afiskon/hbr-8b/images/front-panel.jpg

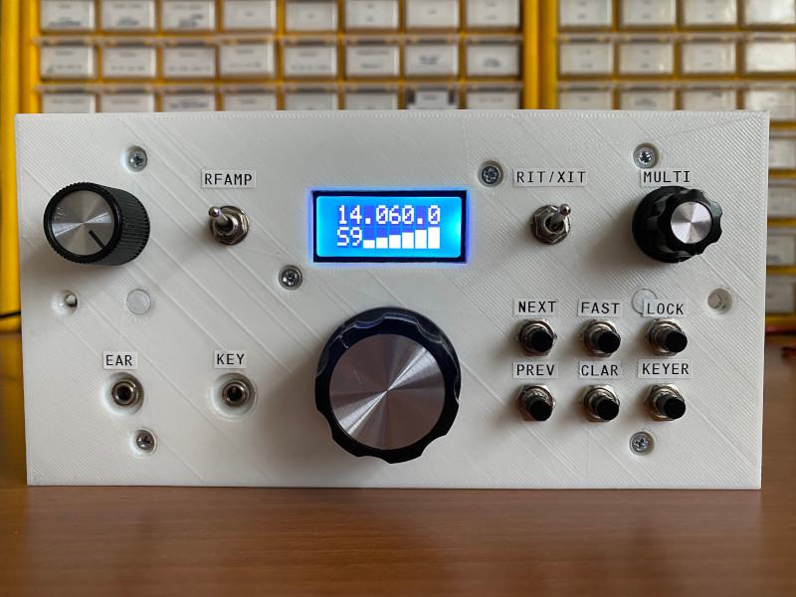
images/front-panel.jpg
