afiskon/hbr-8b/images/bpfs/10.png

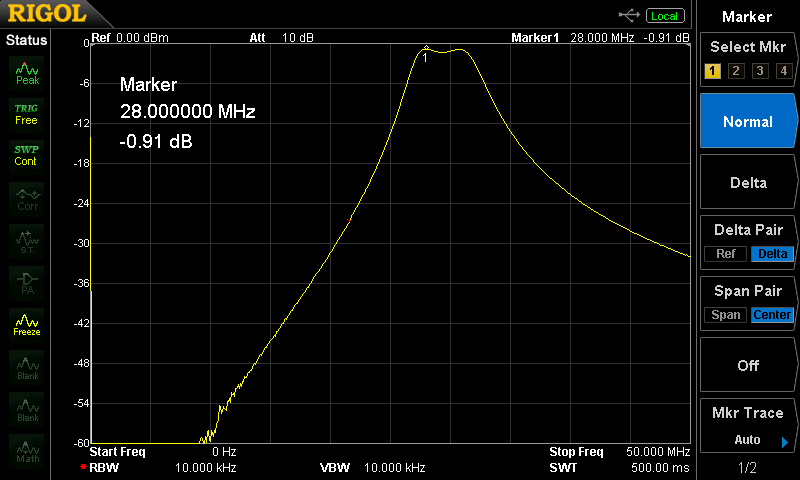
images/bpfs/10.png
