afiskon/hbr-8b/images/bpfs/12.png

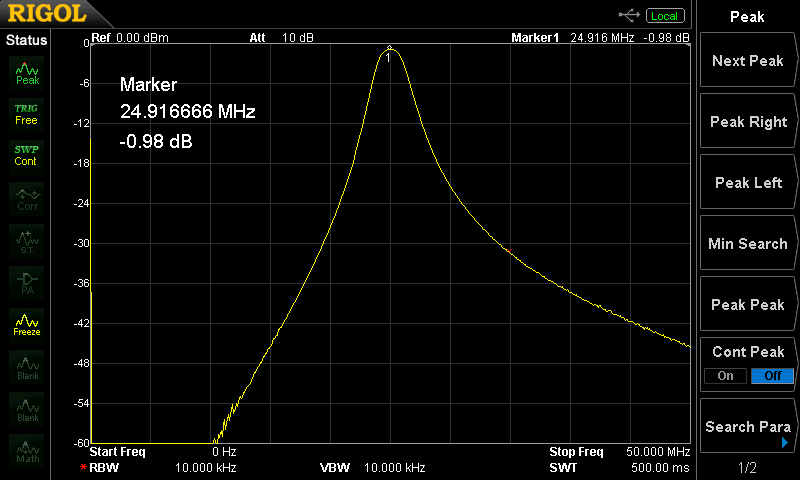
images/bpfs/12.png
