afiskon/hbr-8b/images/bpfs/15.png

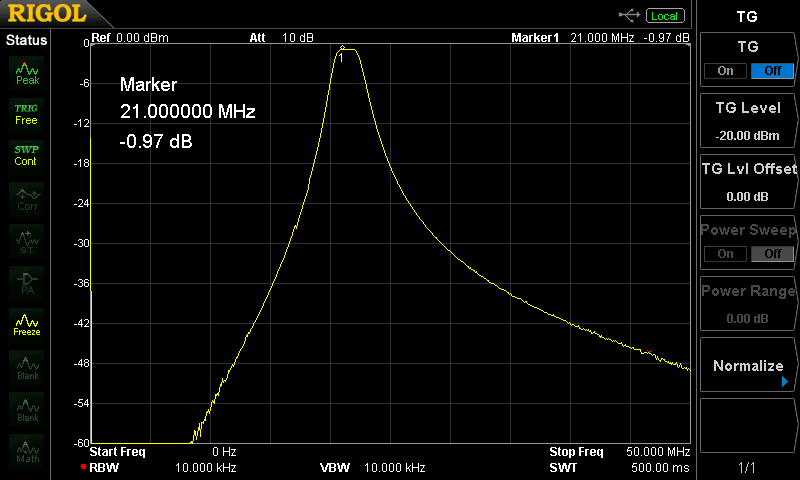
images/bpfs/15.png
