afiskon/hbr-8b/images/bpfs/17.png

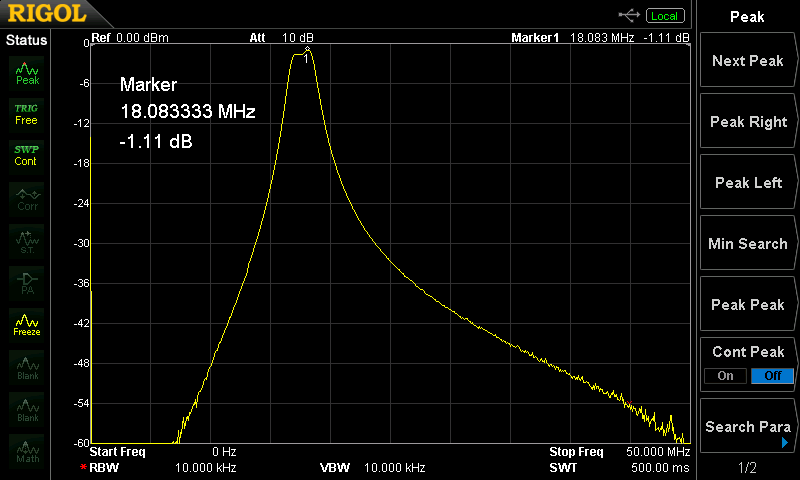
images/bpfs/17.png
