afiskon/hbr-8b/images/bpfs/20.png

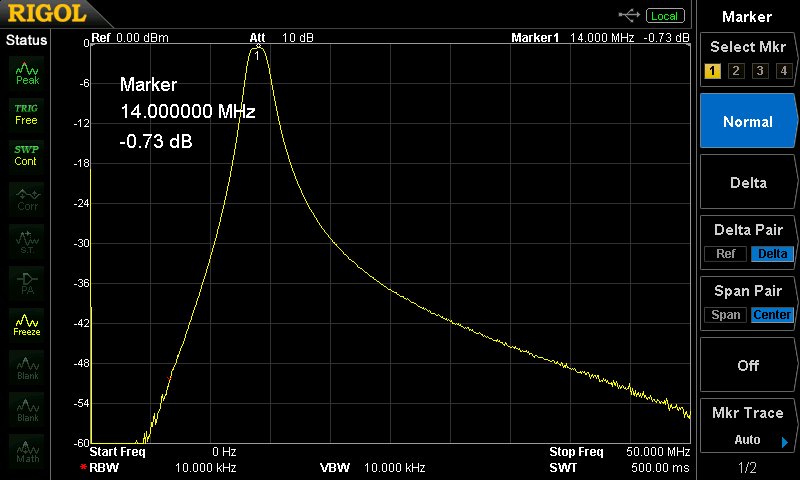
images/bpfs/20.png
