afiskon/hbr-8b/images/bpfs/30.png

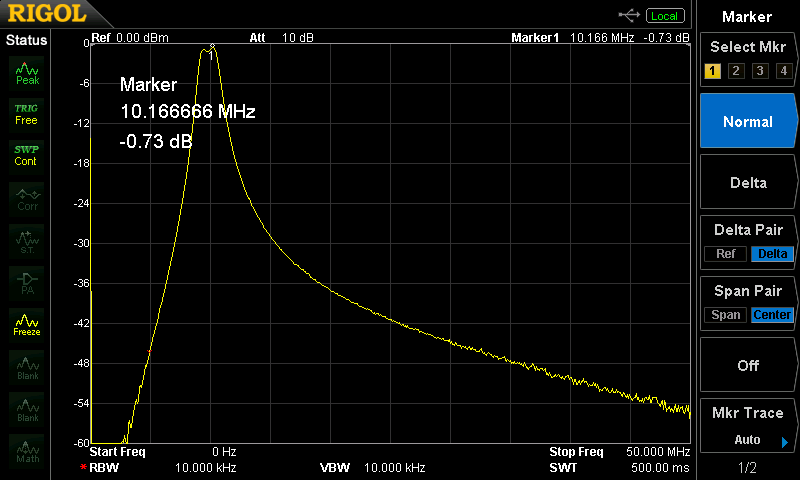
images/bpfs/30.png
