afiskon/hbr-8b/images/bpfs/40.png

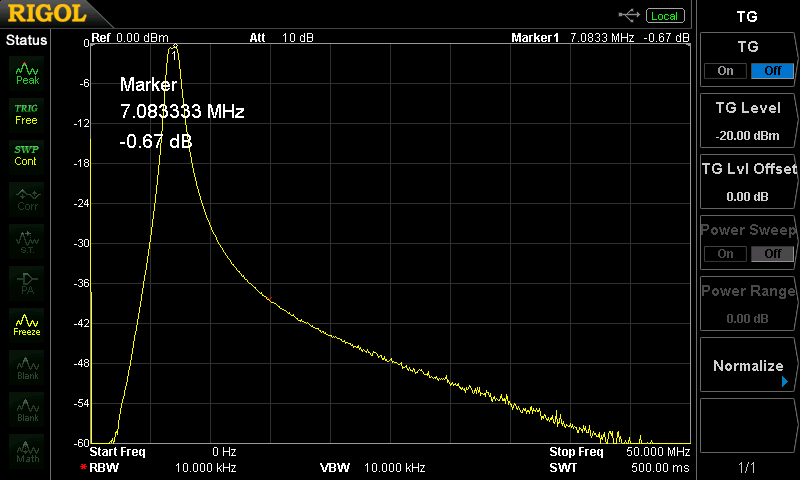
images/bpfs/40.png
