afiskon/hbr-8b/images/bpfs/80.png

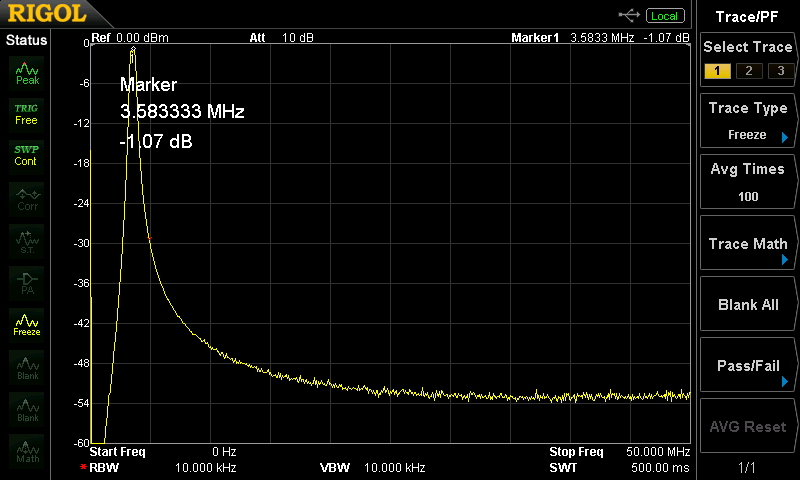
images/bpfs/80.png
