afiskon/hbr-8b/images/harmonics/10.png

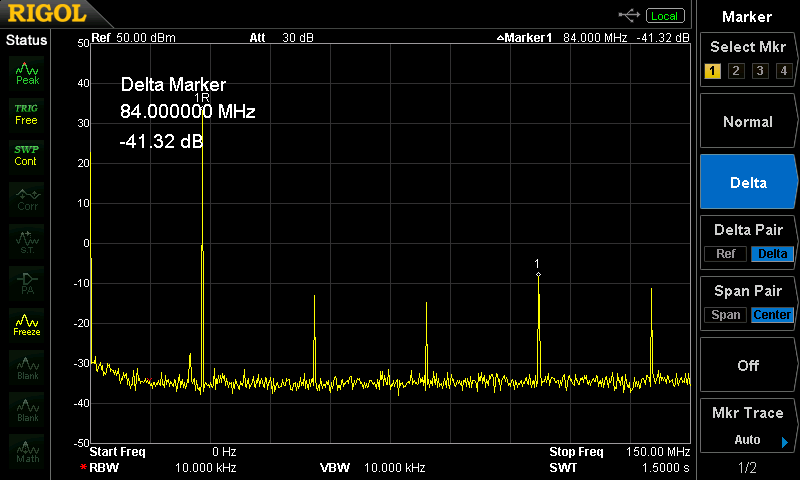
images/harmonics/10.png
