afiskon/hbr-8b/images/harmonics/12.png

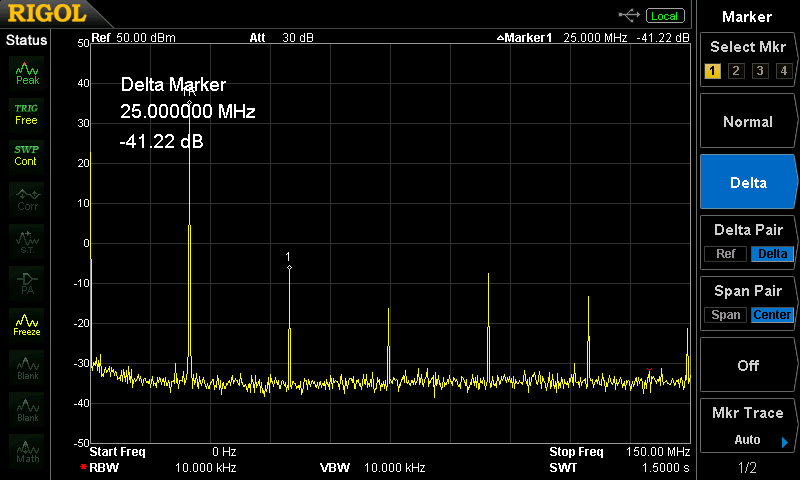
images/harmonics/12.png
