afiskon/hbr-8b/images/harmonics/15.png

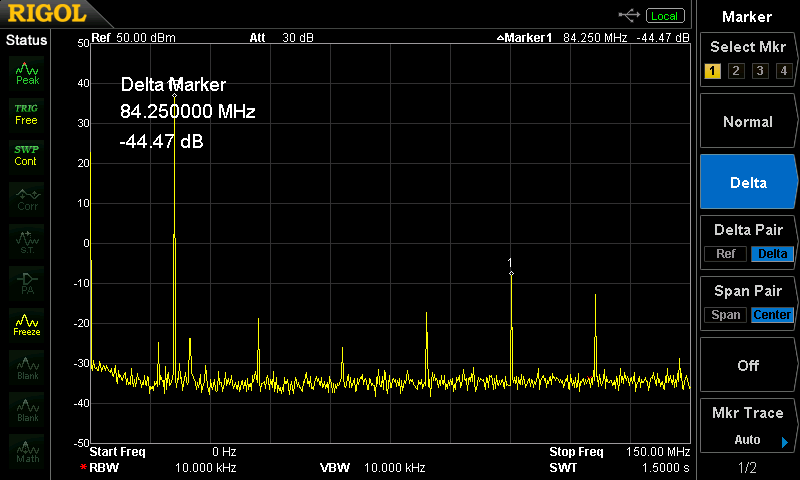
images/harmonics/15.png
