afiskon/hbr-8b/images/harmonics/17.png

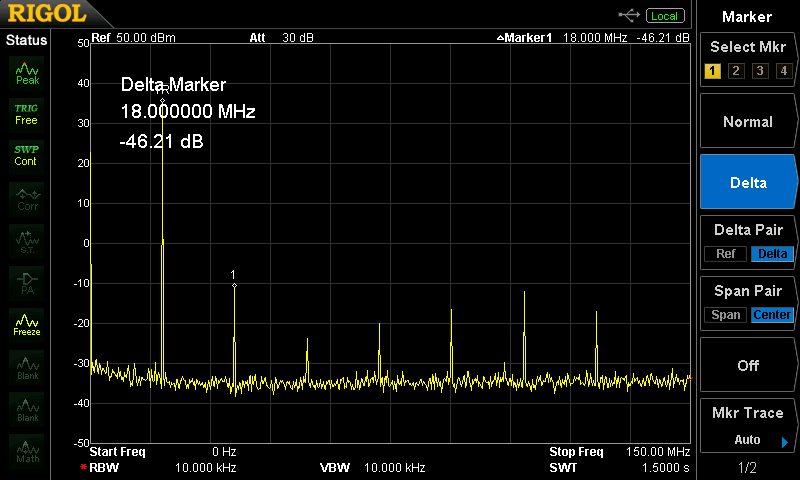
images/harmonics/17.png
