afiskon/hbr-8b/images/harmonics/20.png

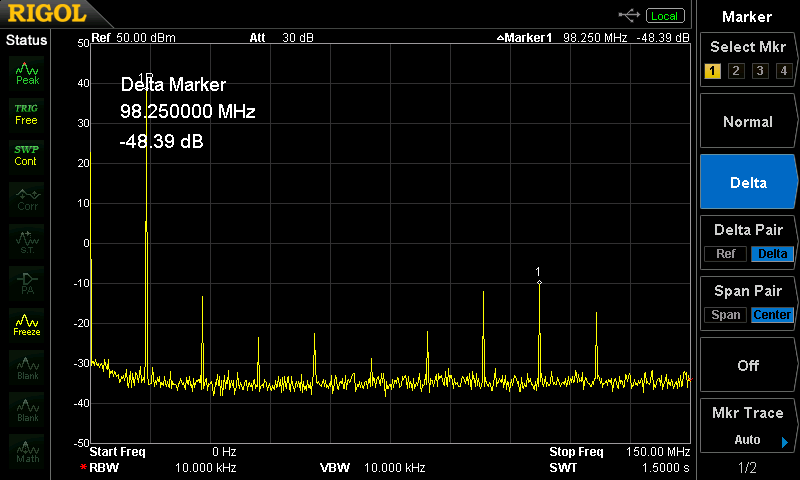
images/harmonics/20.png
