afiskon/hbr-8b/images/harmonics/30.png

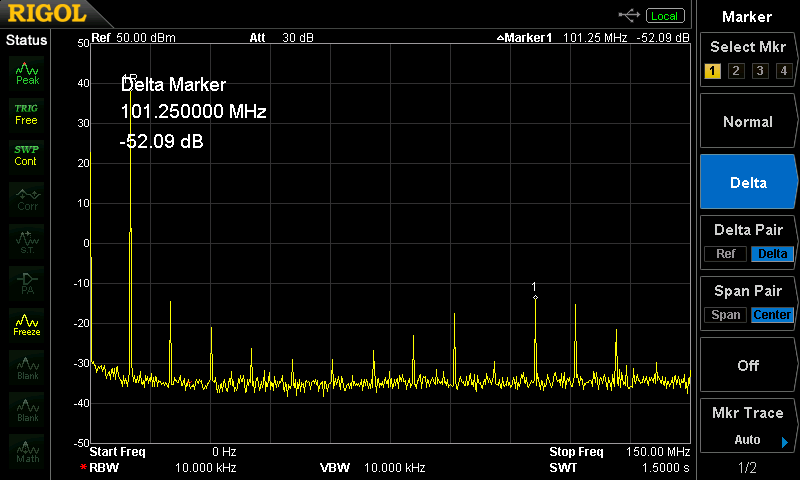
images/harmonics/30.png
