afiskon/hbr-8b/images/harmonics/40.png

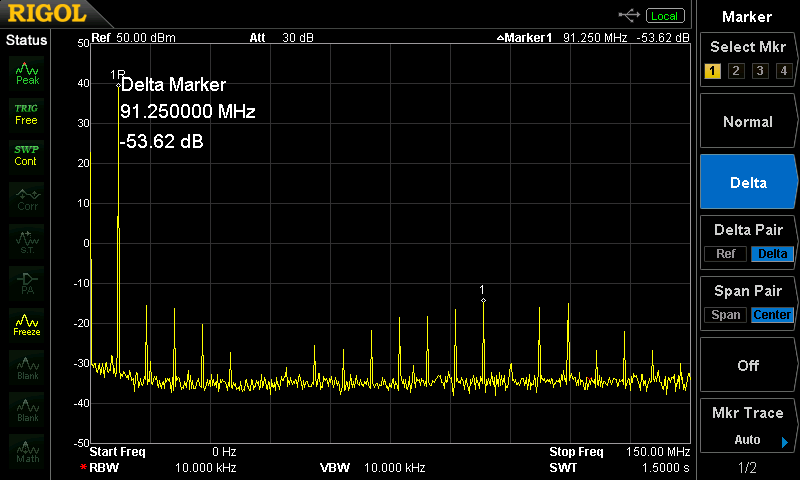
images/harmonics/40.png
