afiskon/hbr-8b/images/harmonics/80.png

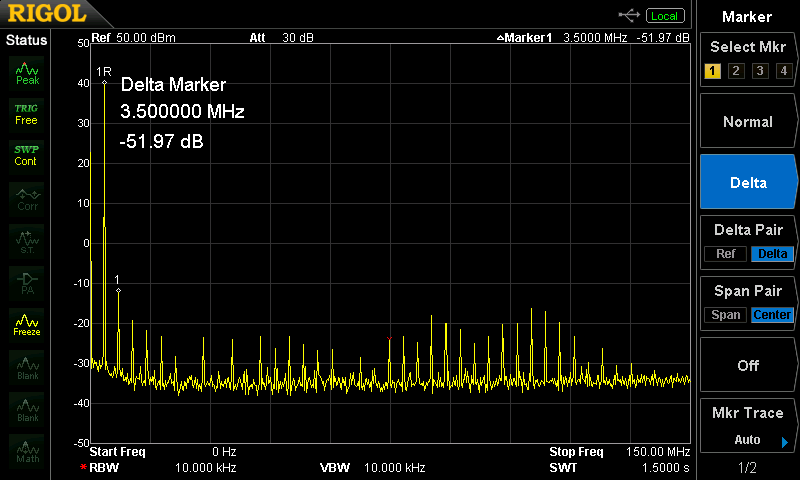
images/harmonics/80.png
