afiskon/hbr-8b/images/lpfs/lpf-80.png

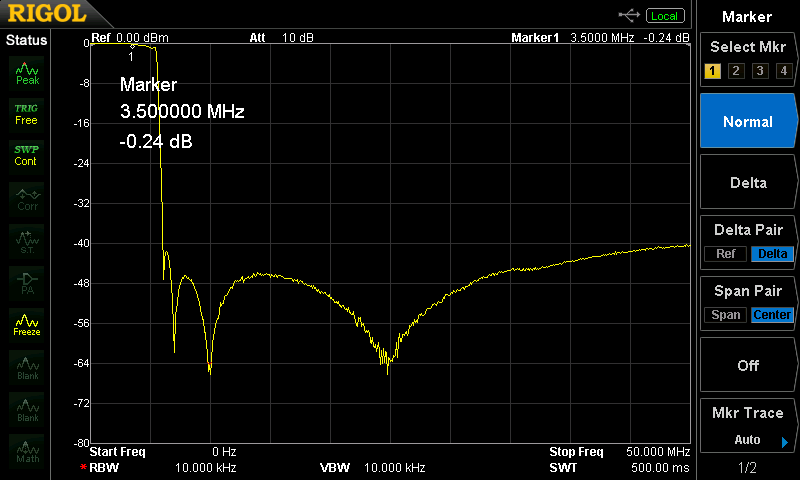
images/lpfs/lpf-80.png
