afiskon/hbr-8b/images/lpfs/lpf-2017.png

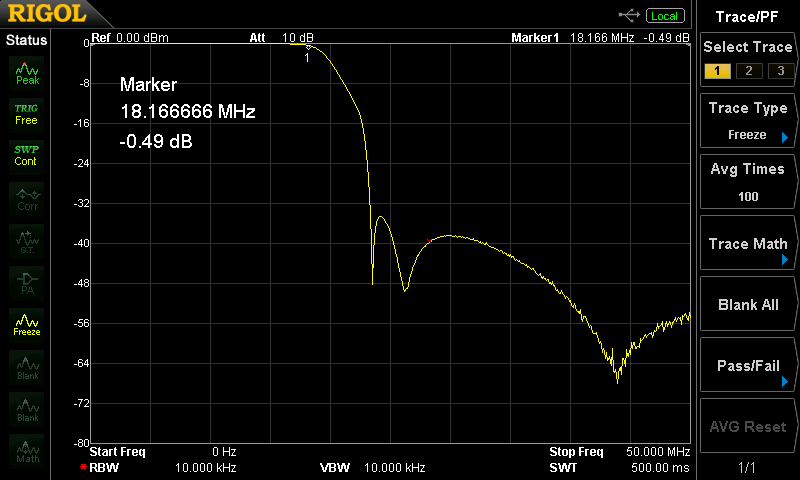
images/lpfs/lpf-2017.png
