afiskon/hbr-8b/images/lpfs/lpf-4030.png

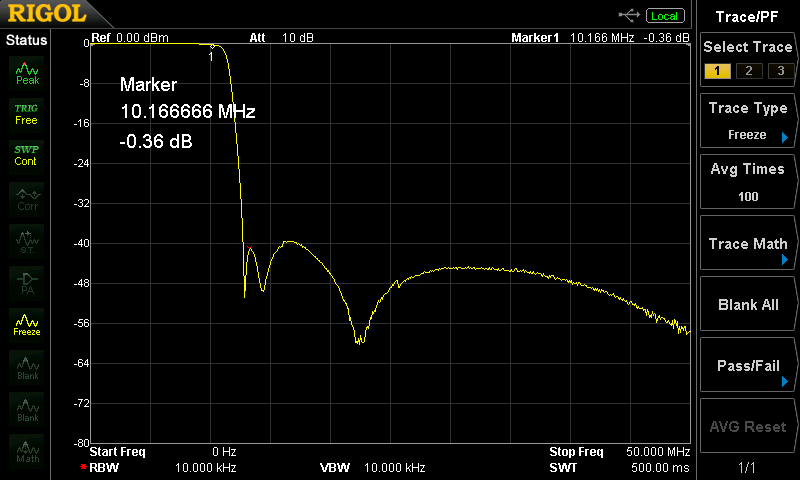
images/lpfs/lpf-4030.png
