afiskon/hbr-8b/images/power/10.png

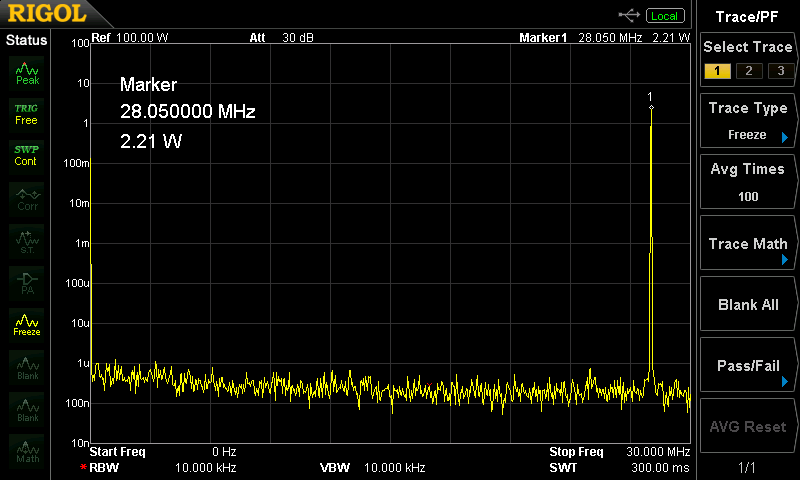
images/power/10.png
