afiskon/hbr-8b/images/power/12.png

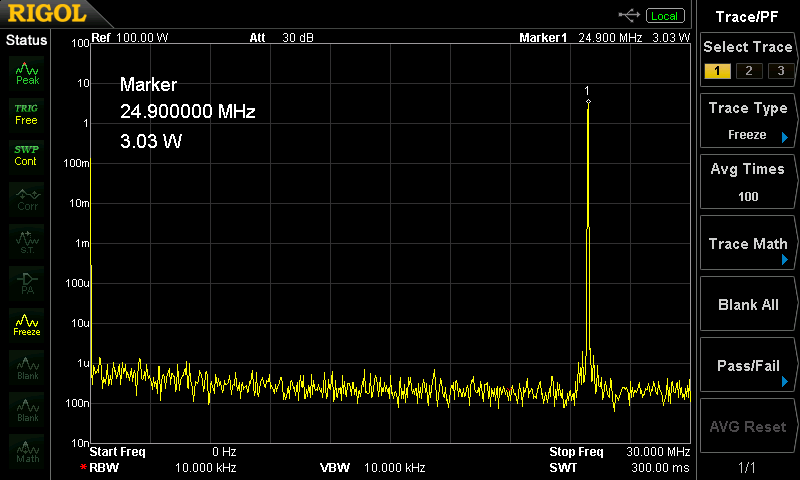
images/power/12.png
