afiskon/hbr-8b/images/power/15.png

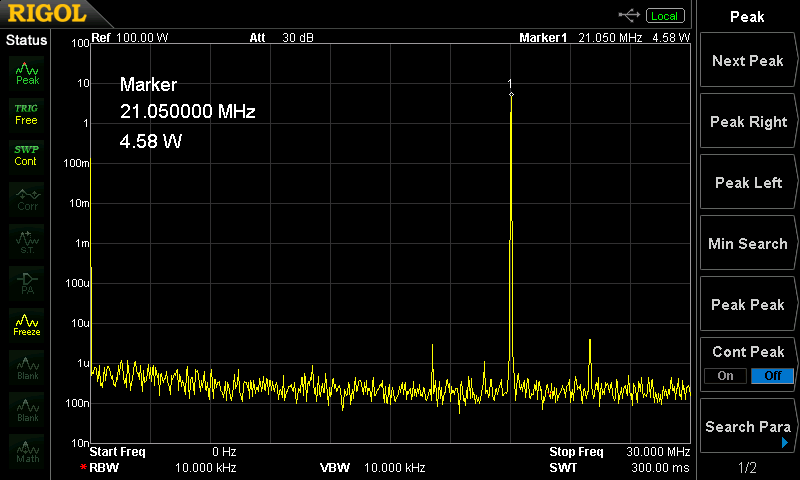
images/power/15.png
