afiskon/hbr-8b/images/power/17.png

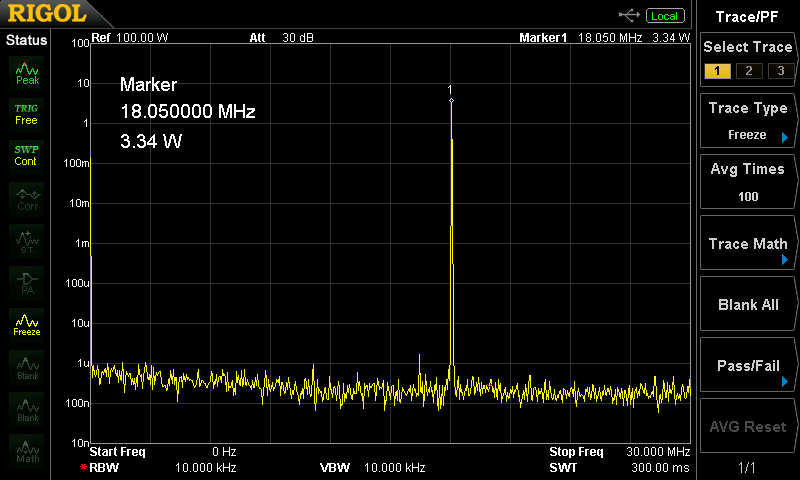
images/power/17.png
