afiskon/hbr-8b/images/power/20.png

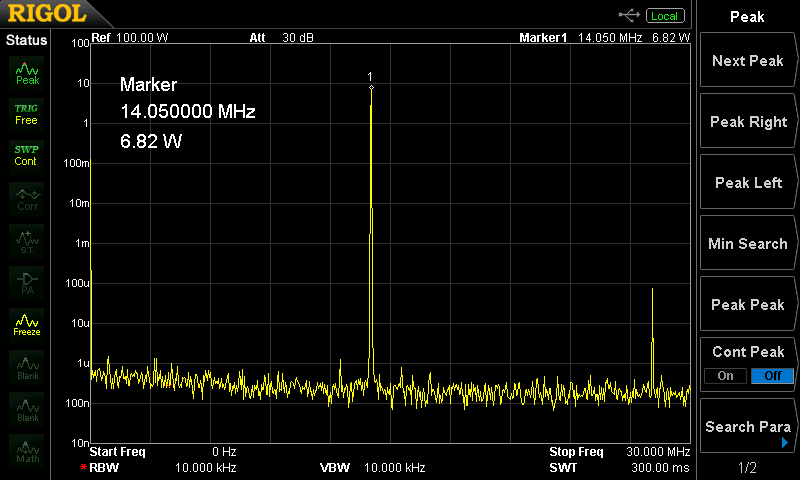
images/power/20.png
