afiskon/hbr-8b/images/power/30.png

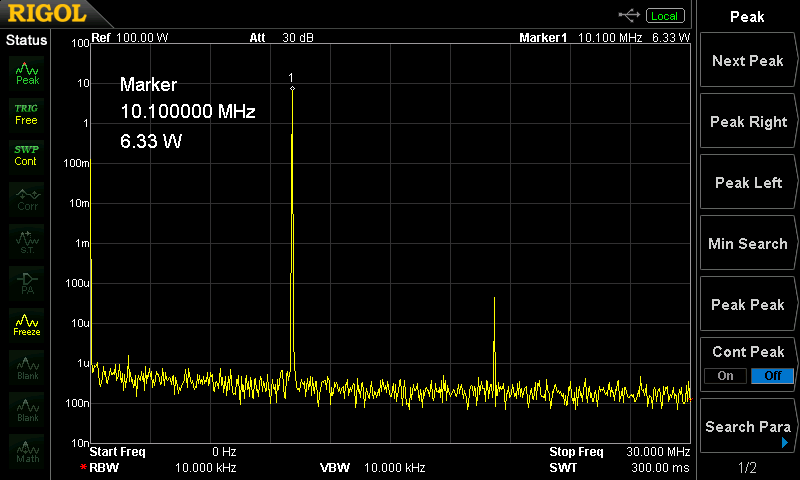
images/power/30.png
