afiskon/hbr-8b/images/power/40.png

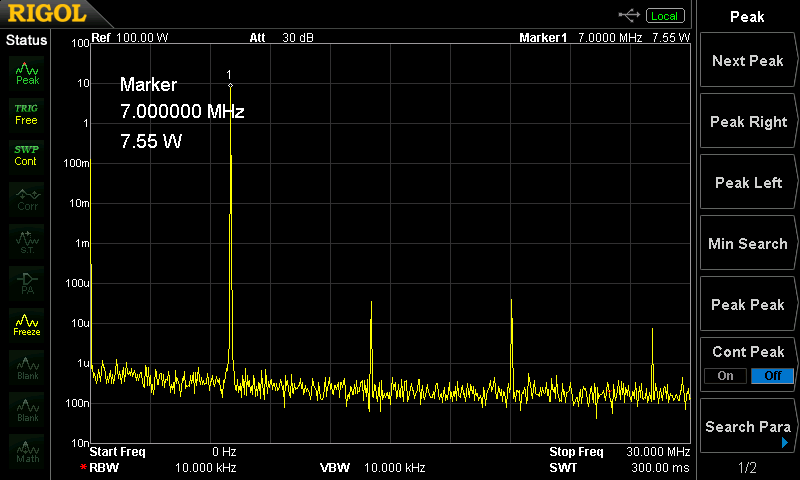
images/power/40.png
