afiskon/hbr-8b/images/power/80.png

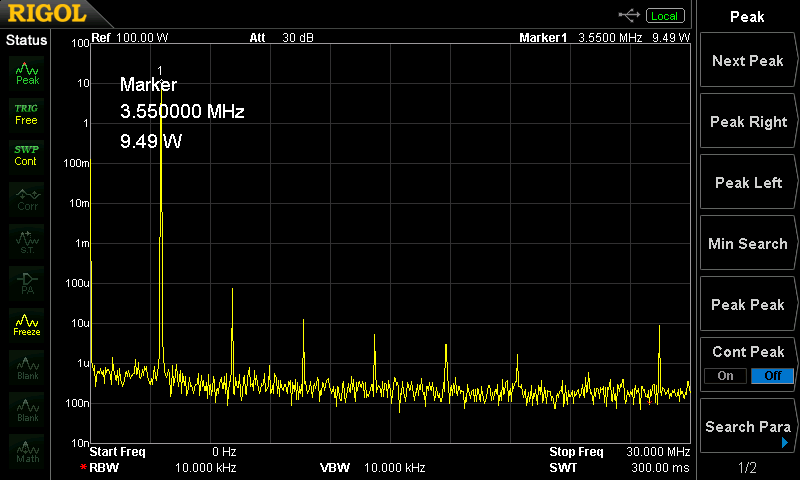
images/power/80.png
